online-junkie/SmHodule/SmHodule/user/cgi/cgiWeather.h

/*
 * cgiWeather.h
 *
 *  Created on: 21.03.2015
 *      Author: k4546
 */

#ifndef USER_CGI_CGIWEATHER_H_
#define USER_CGI_CGIWEATHER_H_


void tplWeather(HttpdConnData *connData, char *token, void **arg);


#endif /* USER_CGI_CGIWEATHER_H_ */
