online-junkie/SmHodule/SmHodule/user/cgi/cgiwifi.h

#ifndef CGIWIFI_H
#define CGIWIFI_H

#include "httpd.h"

int cgiWiFiScan(HttpdConnData *connData);
void tplWlan(HttpdConnData *connData, char *token, void **arg);
int cgiWiFi(HttpdConnData *connData);
int cgiWiFiConnect(HttpdConnData *connData);
int cgiWiFiApReset(HttpdConnData *connData);
int cgiWifiSetMode(HttpdConnData *connData);

#endif
